dusjagr/SolarpunkSynth/SolarPunkSynth/MASK/SolarpunkSynth_empty.png

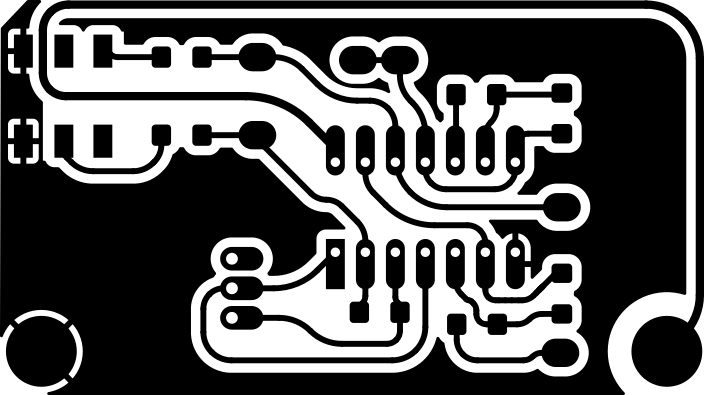
SolarPunkSynth/MASK/SolarpunkSynth_empty.png
