dusjagr/SolarpunkSynth/SolarSynth_digilog/DIY_pcb/SolarSynth_MASK.png

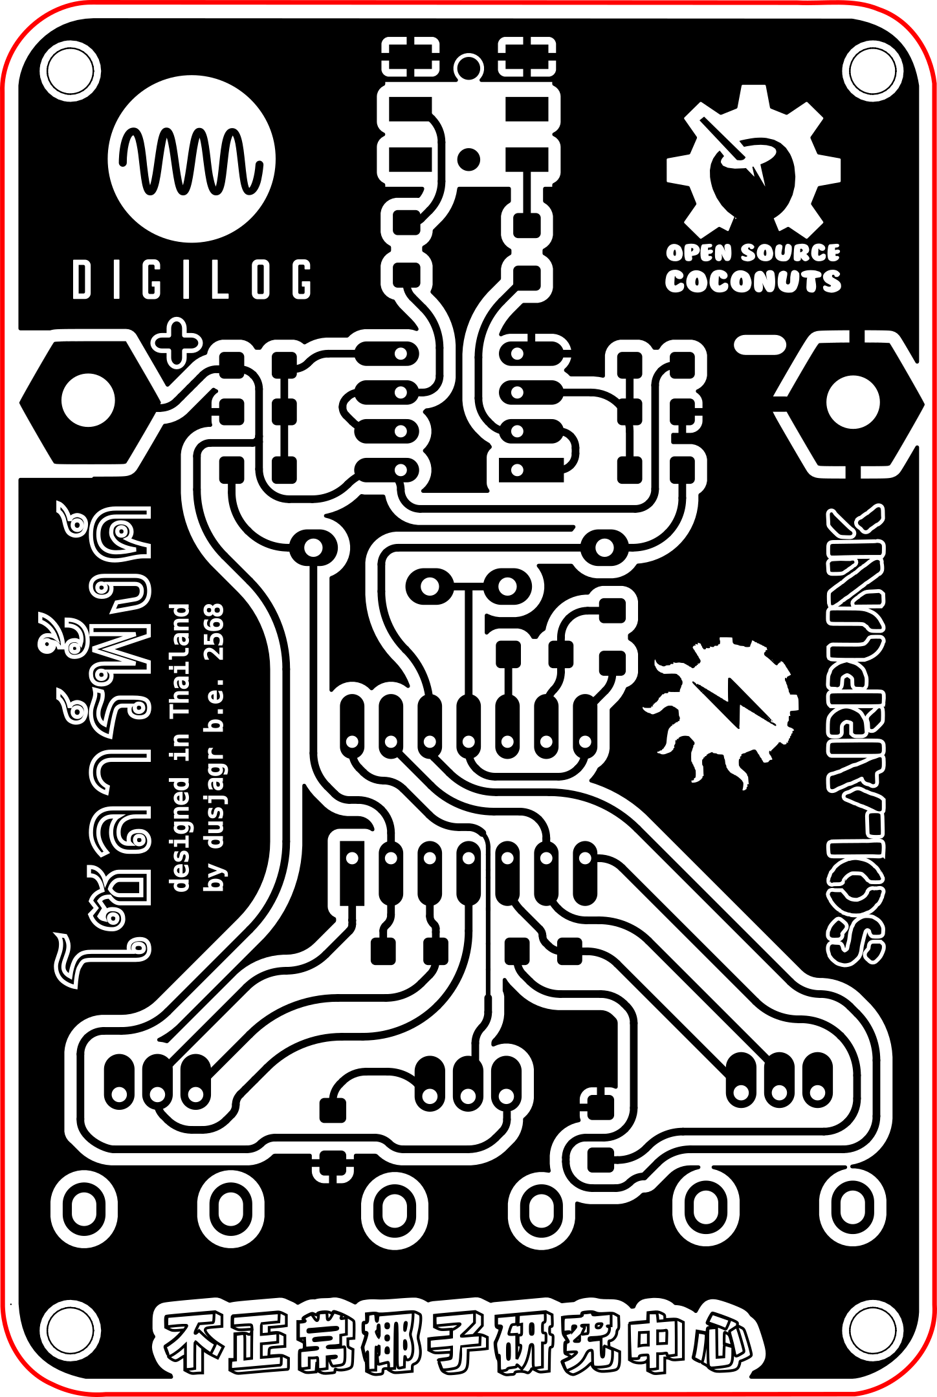
SolarSynth_digilog/DIY_pcb/SolarSynth_MASK.png
